ralucaguceanu/e-book-tsc/Images/Display.png

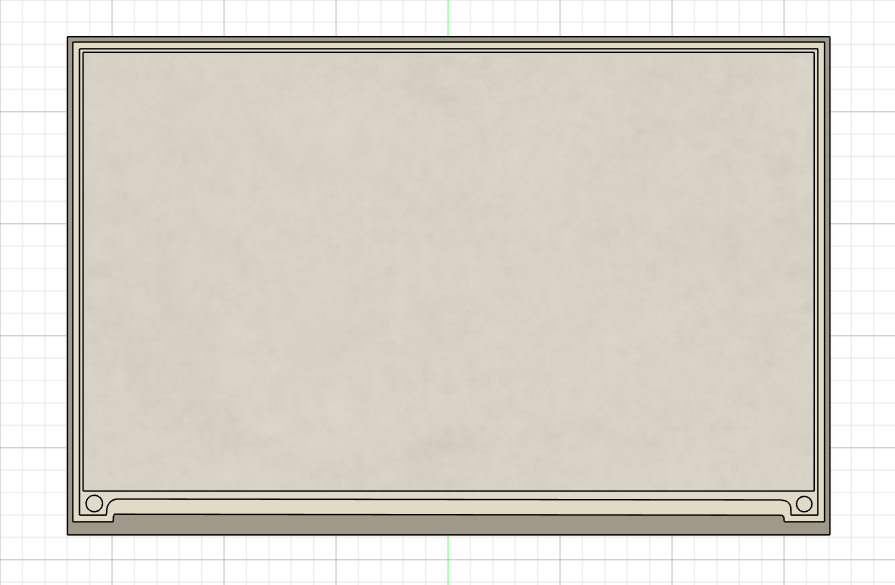
Images/Display.png
