ralucaguceanu/e-book-tsc/Images/Full-Lateral-View-Top.png

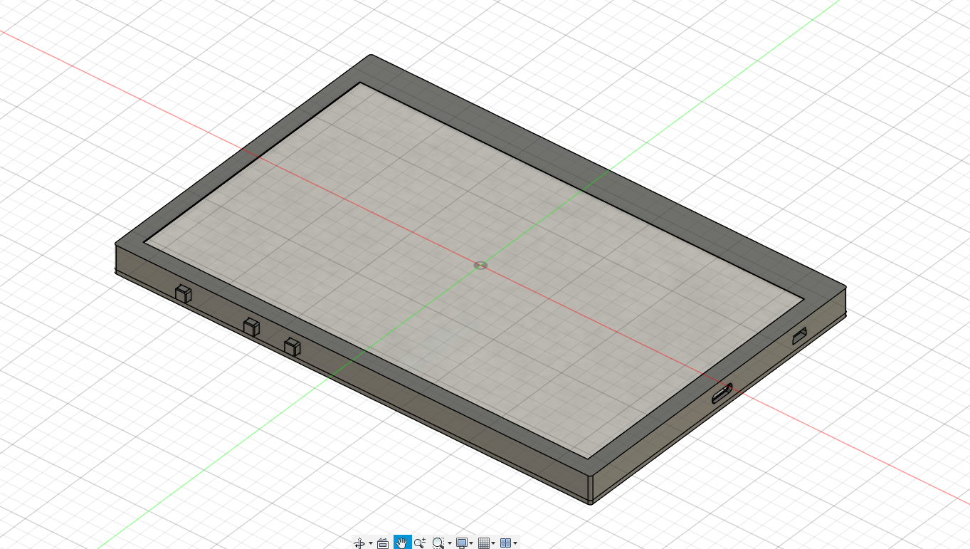
Images/Full-Lateral-View-Top.png
